TinyCircuits/TinyCircuits-TinyShield-Ambient_Light-ASD2811/images/ASD2811-Tutorial-Image-05.png

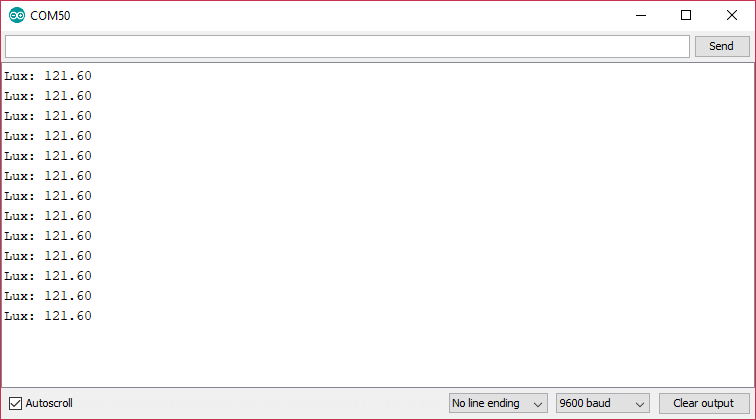
images/ASD2811-Tutorial-Image-05.png
